Apfelwurm/minivolumidi/img/IMG_20210830_220738968.jpg

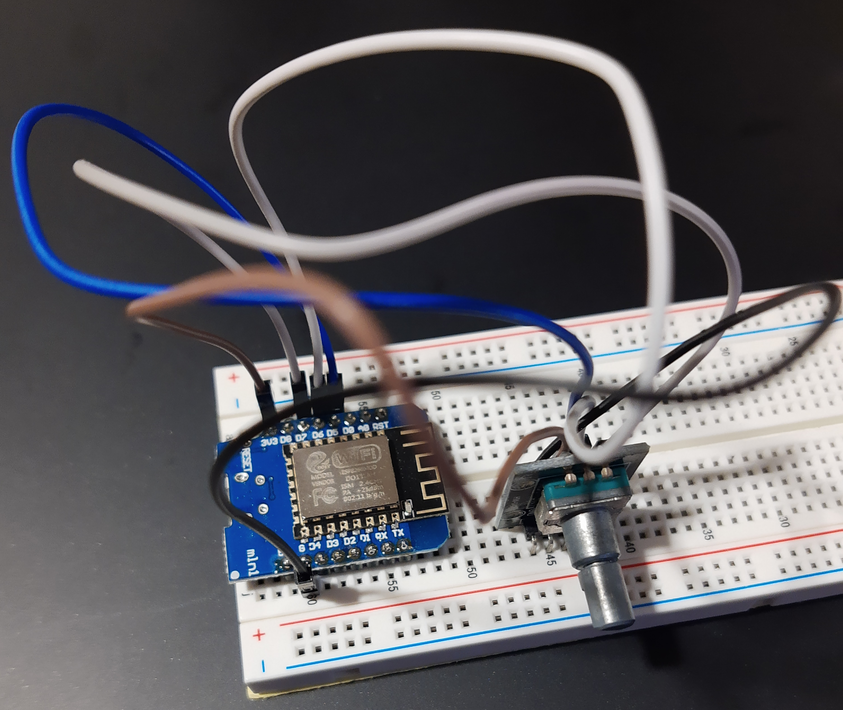
img/IMG_20210830_220738968.jpg
