Apfelwurm/minivolumidi/img/IMG_20210830_220804597.jpg

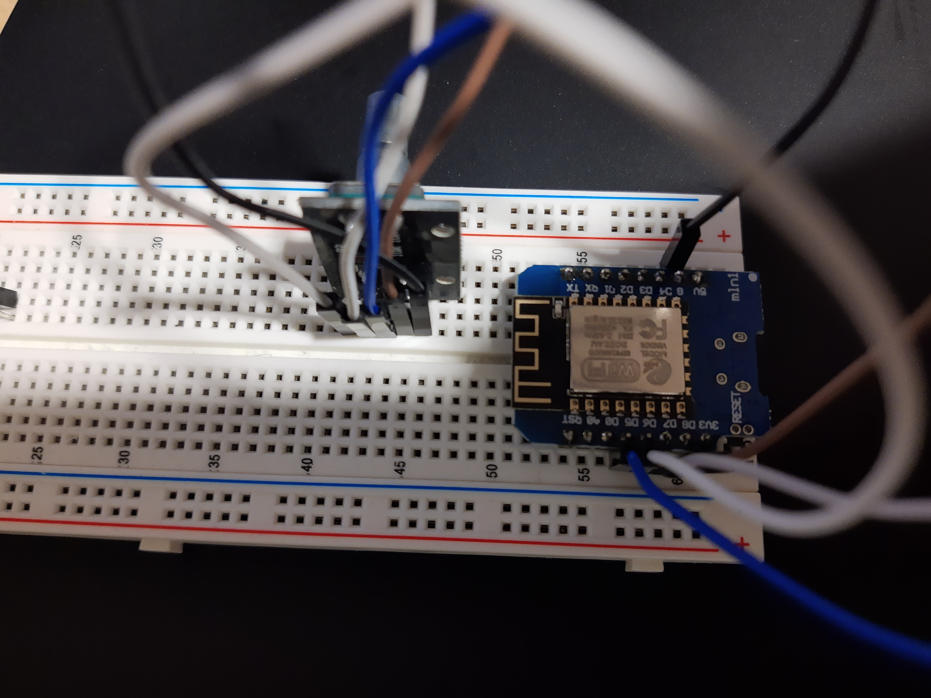
img/IMG_20210830_220804597.jpg
