Apfelwurm/minivolumidi/img/IMG_20210830_220931732.jpg

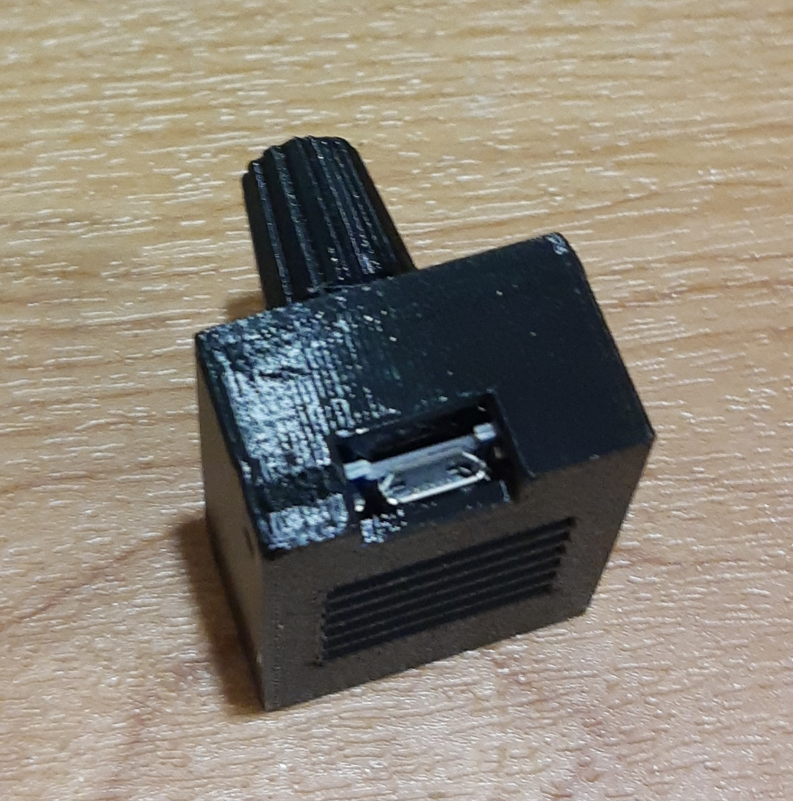
img/IMG_20210830_220931732.jpg
