Apfelwurm/minivolumidi/img/IMG_20210830_221226090.jpg

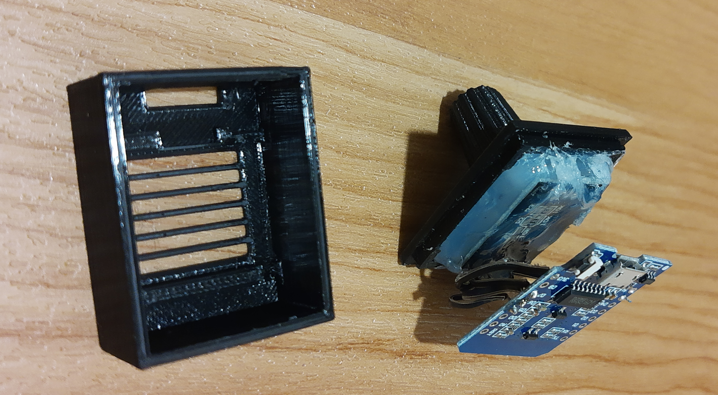
img/IMG_20210830_221226090.jpg
