Apfelwurm/minivolumidi/img/IMG_20210830_221316768.jpg

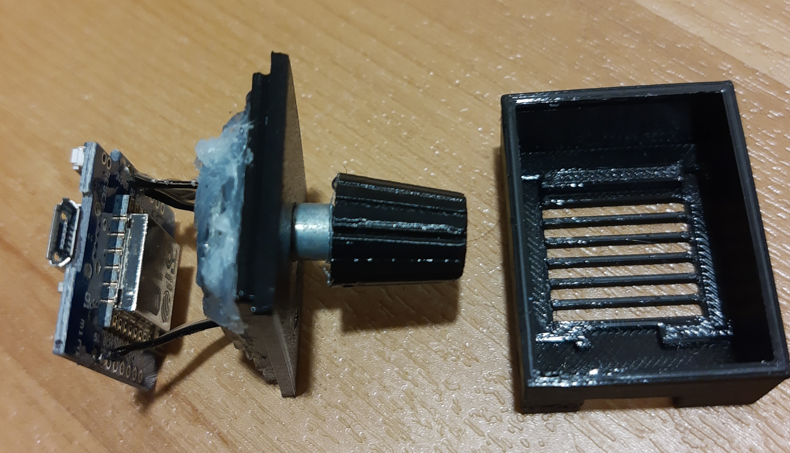
img/IMG_20210830_221316768.jpg
